thesunRider/RFGen/labRF_Kicad/labRF/labRF.kicad_sch

## KiCad design labRF_Kicad/labRF/labRF.kicad_sch (2024-09-11)

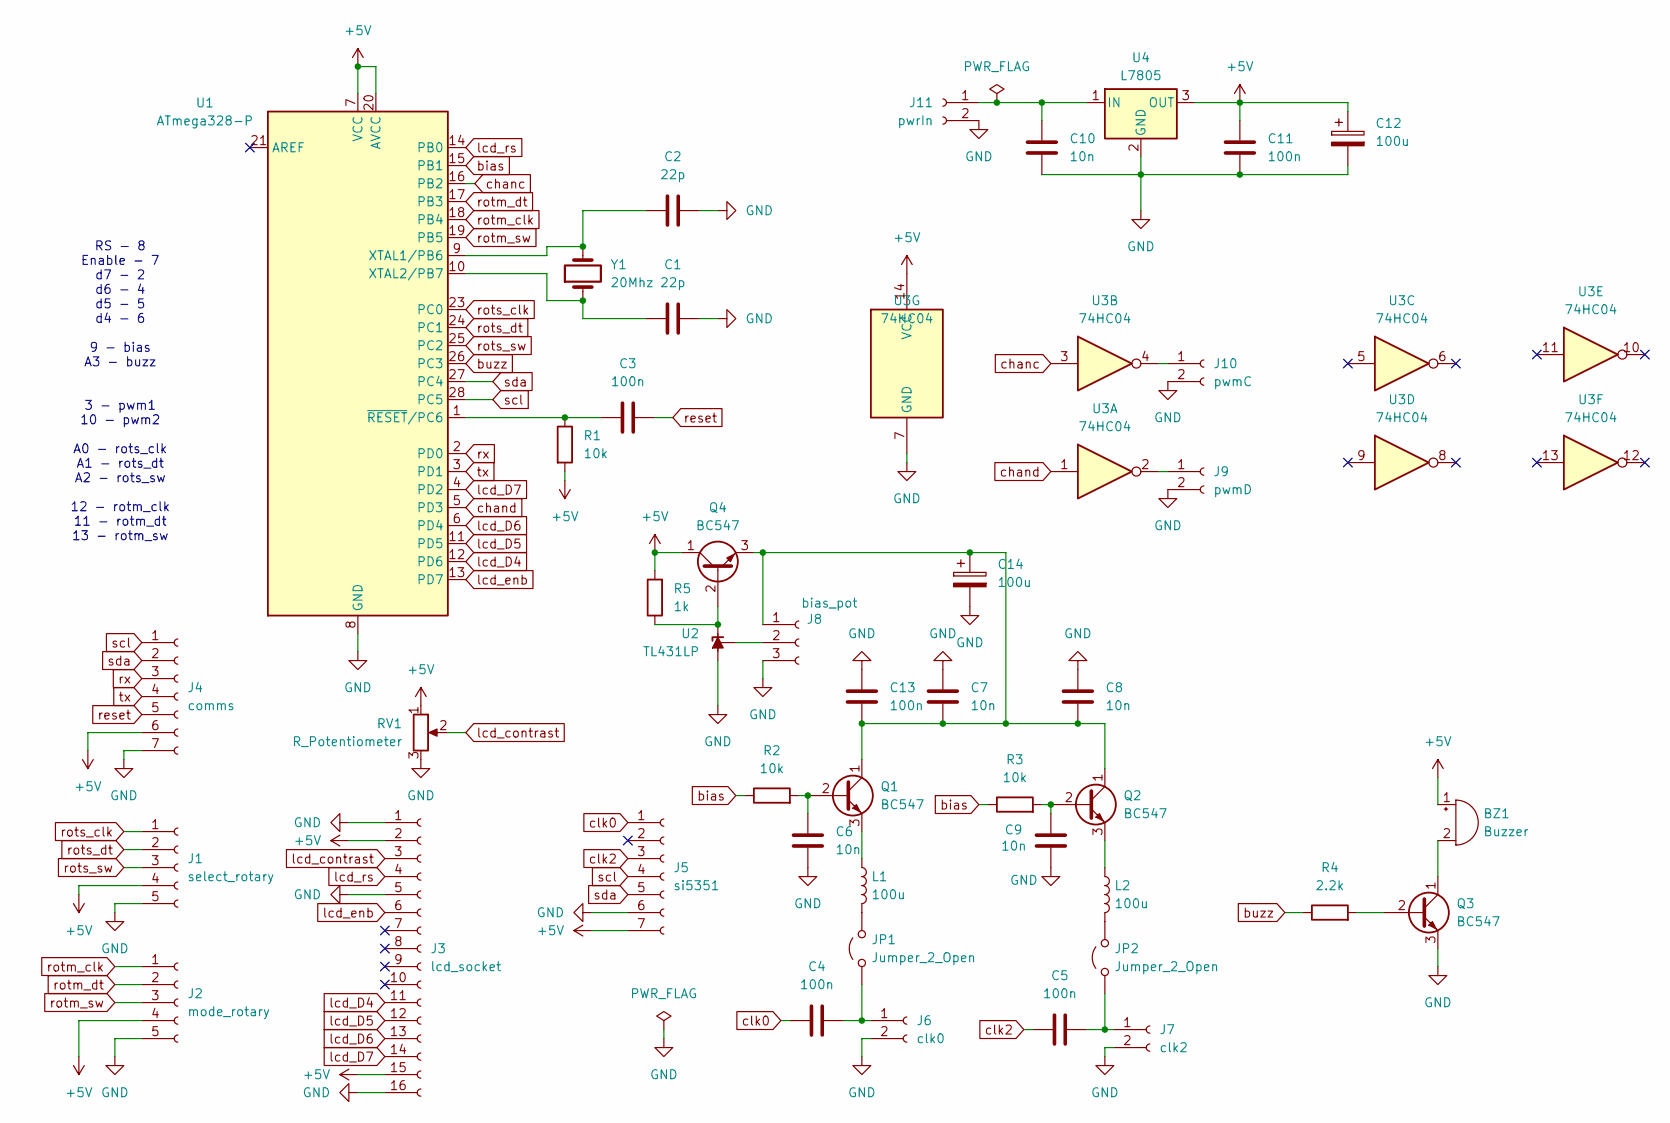
[picture p11: schematic labRF.kicad_sch]

Parts:
BZ1: Buzzer; Buzzer_D14mm_H7mm_P10mm
C1, C2: 22p; C_Disc_D5.0mm_W2.5mm_P2.50mm
C3, C4, C5, C11, C13: 100n; C_Disc_D5.0mm_W2.5mm_P2.50mm
C6, C7, C8, C9, C10: 10n; C_Disc_D5.0mm_W2.5mm_P2.50mm
C12, C14: 100u; CP_Radial_D8.0mm_P5.00mm
J1: select_rotary; PinHeader_1x05_P2.54mm_Vertical
J2: mode_rotary; PinHeader_1x05_P2.54mm_Vertical
J3: lcd_socket; PinHeader_1x16_P2.54mm_Vertical
J4: comms; PinHeader_1x07_P2.54mm_Vertical
J5: si5351; PinHeader_1x07_P2.54mm_Vertical
J6: clk0; PinHeader_1x02_P2.54mm_Vertical
J7: clk2; PinHeader_1x02_P2.54mm_Vertical
J8: bias_pot; FanPinHeader_1x03_P2.54mm_Vertical
J9: pwmD; PinHeader_1x02_P2.54mm_Vertical
J10: pwmC; PinHeader_1x02_P2.54mm_Vertical
J11: pwrIn; PinHeader_1x02_P2.54mm_Vertical
JP1, JP2: Jumper_2_Open; PinHeader_1x02_P2.54mm_Vertical
L1, L2: 100u; L_Toroid_Vertical_L14.7mm_W8.6mm_P5.58mm_Pulse_KM-1
Q1, Q2, Q3, Q4: BC547; TO-92_Inline
R1, R2, R3: 10k; R_Axial_DIN0207_L6.3mm_D2.5mm_P10.16mm_Horizontal
R4: 2.2k; R_Axial_DIN0207_L6.3mm_D2.5mm_P10.16mm_Horizontal
R5: 1k; R_Axial_DIN0207_L6.3mm_D2.5mm_P10.16mm_Horizontal
RV1: R_Potentiometer; Potentiometer_Bourns_3386P_Vertical
U1: ATmega328-P; DIP-28_W7.62mm
U2: TL431LP; TO-92_Inline
U3: 74HC04; DIP-14_W7.62mm
U4: L7805; TO-220-3_Vertical
Y1: 20Mhz; Crystal_HC49-U_Vertical

Connections:
+5V: BZ1.1 (+), C11.2, C12.1, J1.4, J2.4, J3.2, J3.15, J4.6, J5.7, Q4.1 (C), R1.2, R5.2, RV1.1, U1.7 (VCC), U1.20 (AVCC), U3.14 (VCC), U4.3 (OUT)
GND: C1.2, C2.2, C6.2, C7.1, C8.1, C9.2, C10.1, C11.1, C12.2, C13.1, C14.2, J1.5, J2.5, J3.1, J3.5, J3.16, J4.7, J5.6, J6.2, J7.2, J8.3, J9.2, J10.2, J11.2, Q3.3 (E), RV1.3, U1.8 (GND), U1.22 (GND), U2.2 (A), U3.7 (GND), U4.2 (GND)
unnamed: BZ1.2 (-), Q3.1 (C)
unnamed: C1.1, U1.10 (XTAL2/PB7), Y1.1
unnamed: C2.1, U1.9 (XTAL1/PB6), Y1.2
unnamed: C3.1, R1.1, U1.1 (~RESET/PC6)
unnamed: C4.2, J6.1, JP1.1 (A)
unnamed: C5.2, J7.1, JP2.1 (A)
unnamed: C6.1, Q1.2 (B), R2.2
unnamed: C9.1, Q2.2 (B), R3.2
unnamed: C10.2, J11.1, U4.1 (IN)
unnamed: C7.2, C8.2, C13.2, C14.1, J8.1, Q1.1 (C), Q2.1 (C), Q4.3 (E)
unnamed: J8.2, U2.1 (REF)
unnamed: J9.1, U3.2
unnamed: J10.1, U3.4
unnamed: JP1.2 (B), L1.2
unnamed: JP2.2 (B), L2.2
unnamed: L1.1, Q1.3 (E)
unnamed: L2.1, Q2.3 (E)
unnamed: Q3.2 (B), R4.2
unnamed: Q4.2 (B), R5.1, U2.3 (K)
bias: R2.1, R3.1, U1.15 (PB1)
buzz: R4.1, U1.26 (PC3)
chanc: U1.16 (PB2), U3.3
chand: U1.5 (PD3), U3.1
clk0: C4.1, J5.1
clk2: C5.1, J5.3
lcd_D4: J3.11, U1.12 (PD6)
lcd_D5: J3.12, U1.11 (PD5)
lcd_D6: J3.13, U1.6 (PD4)
lcd_D7: J3.14, U1.4 (PD2)
lcd_contrast: J3.3, RV1.2
lcd_enb: J3.6, U1.13 (PD7)
lcd_rs: J3.4, U1.14 (PB0)
reset: C3.2, J4.5
rotm_clk: J2.1, U1.18 (PB4)
rotm_dt: J2.2, U1.17 (PB3)
rotm_sw: J2.3, U1.19 (PB5)
rots_clk: J1.1, U1.23 (PC0)
rots_dt: J1.2, U1.24 (PC1)
rots_sw: J1.3, U1.25 (PC2)
rx: J4.3, U1.2 (PD0)
scl: J4.1, J5.4, U1.28 (PC5)
sda: J4.2, J5.5, U1.27 (PC4)
tx: J4.4, U1.3 (PD1)

Notes on the sheet:
RS - 8 Enable - 7 d7 - 2 d6 - 4 d5 - 5 d4 - 6 9 - bias A3 - buzz 3 - pwm1 10 - pwm2 A0 - rots_clk A1 - rots_dt A2 - rots_sw 12 - rotm_clk 11 - rotm_dt 13 - rotm_sw
