thesunRider/RFGen/sketches/bluepill/main/src/RFM119/HopeDuino_CMT211xA.cpp

/*
 * THE FOLLOWING FIRMWARE IS PROVIDED: 
 *  (1) "AS IS" WITH NO WARRANTY; 
 *  (2) TO ENABLE ACCESS TO CODING INFORMATION TO GUIDE AND FACILITATE CUSTOMER.
 * CONSEQUENTLY, HopeRF SHALL NOT BE HELD LIABLE FOR ANY DIRECT, INDIRECT OR
 * CONSEQUENTIAL DAMAGES WITH RESPECT TO ANY CLAIMS ARISING FROM THE CONTENT
 * OF SUCH FIRMWARE AND/OR THE USE MADE BY CUSTOMERS OF THE CODING INFORMATION
 * CONTAINED HEREIN IN CONNECTION WITH THEIR PRODUCTS.
 * 
 * Copyright (C) HopeRF
 *
 * website: www.HopeRF.com
 *          www.HopeRF.cn     
 */

/*! 
 * file       HopeDuino_CMT211xA.cpp
 * brief      driver for CMT211xA 
 * hardware   HopeDuino with RFM11x
 *            
 *
 * version    1.0
 * date       Feb 18 2016
 * author     QY Ruan
 */

#include "HopeDuino_CMT211xA.h"

/**********************************************************
 **Name:     vCMT211xAInit
 **Function: Init. CMT211xA
 **Input:    none
 **Output:   none
 **********************************************************/
void cmt211xaClass::cmt211xaClass::vCMT211xAInit(void) {
  Twi.vTWIInit();

  Twi.vTWIReset(); //step 1
  vSoftReset(); //step 2
  vTwiOff(); //step 3

  ClrTDAT(); //Set Dat to low
  OutputTDAT(); //Read for Tx
}

//added extra
void cmt211xaClass::TWI_RAM1(uint8_t addr, uint16_t data)
{	
	Twi.vTWIWrite(0x18, addr);
	Twi.vTWIWrite(0x19, data&0xff);
	Twi.vTWIWrite(0x1A, data>>8);
	Twi.vTWIWrite(0x25, 0x01);
}

void cmt211xaClass::turnOnRadio(void) {
  
  Twi.vTWIInit();
  Twi.vTWIReset(); //step 1
  vTwiOff(); //step 2
  SetTDAT();
}

void cmt211xaClass::turnOFFRadio(void) {
ClrTDAT();
}

//added extra
//one register remains unclear after a very rudimentary reverse engineering attempt (0x5f1e gets changed at low frequencies - is this critical?
//frequency = 26000000/2^17/prescale*pll_multiple
//prescale can be 1.5, 2, 3 controlled by positions 1 and 6
//gmsk not supported presently
void cmt211xaClass::vChipfrequency(uint32_t freq, uint32_t dev, uint8_t mod) {
  //determine prescale
  uint8_t prescale15;
  uint8_t prescale2;
  if (freq <= 300000000UL) {
    prescale15 = 1;
    prescale2 = 1;
  } else if (freq <= 400000000UL) {
    prescale15 = 0;
    prescale2 = 1;
  } else if (freq <= 600000000UL) {
    prescale15 = 1;
    prescale2 = 0;
  } else {
    prescale15 = 0;
    prescale2 = 0;
  }

  if (prescale15) TWI_RAM1(6, 0x0001);
  if (prescale2) TWI_RAM1(1, 0x5400);

  int8_t psc2 = 0;
  if (prescale15) psc2 -= 1;
  if (prescale2) psc2 += 1;

  //frequency
  uint64_t tmp1 = freq;
  tmp1 <<= 17 + psc2;
  if (prescale15) tmp1 *= 3;
  uint32_t pll = tmp1 / 26000000UL;
  TWI_RAM1(7, pll & 0xffff);
  TWI_RAM1(8, ((pll >> 16) << 8) | 0x08);

  if (mod == 2) {
    //deviation
    tmp1 = dev;
    tmp1 <<= 14 + psc2;
    if (prescale15) tmp1 *= 3;
    pll = tmp1 / 26000000UL;
    pll <<= 3;
    pll &= 0x07f8;
  } else pll = 0; //no deviation in ook
  TWI_RAM1(9, pll);
}

/**********************************************************
 **Name:     vCMT2119AInit
 **Function: Init. CMT2119A with config 
 **Input:    none
 **Output:   none
 **********************************************************/
void cmt211xaClass::vCMT2119AInit(word para[], byte length,uint32_t freq, uint32_t dev, uint8_t mod)  {
  byte i;
  Twi.vTWIInit();

  Twi.vTWIReset(); //step 1
  vSoftReset(); //step 2
  delay(2); //wait more than 1ms		
  vOpenLdoAndOsc(); //step 3
  vActiveRegsister(); //step 4
  vEnableRegMode(); //step 5
  for (i = 0; i < length; i++) //step 6
    vWriteReg(i, para[i]);

  //reprogram frequency
  vChipfrequency(freq, dev, mod);

  vTwiOff(); //step 7	

  ClrTDAT(); //Set Dat to low
  OutputTDAT(); //Read for Tx
}

/**********************************************************
 **Name:     vCMT211xASleep
 **Function: set CMT211xA to sleep
 **Input:    none
 **Output:   none
 **********************************************************/
void cmt211xaClass::vCMT211xASleep(void) {
  Twi.vTWIReset(); //step 1
  vSoftReset(); //step 2
}

/**********************************************************
 **Name:     vCMT2119ASleep
 **Function: set CMT2119A to sleep
 **Input:    none
 **Output:   none
 **********************************************************/
void cmt211xaClass::vCMT2119ASleep(void) {
  vCloseLdoAndOsc(); //step 1
  Twi.vTWIReset(); //step 2
  vSoftReset(); //step 3
}

/**********************************************************
**Name:     vEncode
**Function: encode 
**Input:    ptr��length��etype
            length need less than 64
**Output:   TxBuf
**********************************************************/
void cmt211xaClass::vEncode(byte ptr[], byte length, encodeType etype) {
  byte i, j, k;

  switch (etype) {
  case E527:
    TxBuf[0] = 0x80;
    TxBuf[1] = 0x00;
    TxBuf[2] = 0x00;
    TxBuf[3] = 0x00;
    for (i = 4; i < (4 + (length << 2)); i++) //1XX0
      TxBuf[i] = 0x88;
    k = 4;
    for (j = 0; j < length; j++) {
      for (i = 0x80; i != 0;) {
        if ((ptr[j] & i) != 0)
          TxBuf[k] |= 0x60;
        i >>= 1;
        if ((ptr[j] & i) != 0)
          TxBuf[k] |= 0x06;
        i >>= 1;
        k++;
      }
    }
    TxBufLength = ((length << 2) + 4);
    break;
  case E201:
    for (i = 0; i < 4; i++) //
      TxBuf[i] = 0x00; //4 byte 0x00
    TxBuf[4] = 0x0A; //10 pulse preamble	
    for (i = 5; i < (5 + 2); i++)
      TxBuf[i] = 0xAA;
    TxBuf[i++] = 0x00; //Sync
    TxBuf[i++] = 0x00;
    k = i + (length * 3);
    j = i;
    for (; j < k;) {
      TxBuf[j++] = 0x92; //1x01x01xB
      TxBuf[j++] = 0x49; //01x01x01B
      TxBuf[j++] = 0x24; //x01x01x0B
    }

    for (j = 0; j < length; j++) {
      if ((ptr[j] & 0x80) == 0x00)
        TxBuf[i] |= 0x40;
      if ((ptr[j] & 0x40) == 0x00)
        TxBuf[i] |= 0x08;
      if ((ptr[j] & 0x20) == 0x00)
        TxBuf[i] |= 0x01;
      i++;
      if ((ptr[j] & 0x10) == 0x00)
        TxBuf[i] |= 0x20;
      if ((ptr[j] & 0x08) == 0x00)
        TxBuf[i] |= 0x04;
      i++;
      if ((ptr[j] & 0x04) == 0x00)
        TxBuf[i] |= 0x80;
      if ((ptr[j] & 0x02) == 0x00)
        TxBuf[i] |= 0x10;
      if ((ptr[j] & 0x01) == 0x00)
        TxBuf[i] |= 0x02;
      i++;
    }
    TxBuf[i++] = 0x92;
    TxBufLength = i;
    break;
  case ENRZ:
  default:
    for (i = 0; i < length; i++) //do nothing
      TxBuf[i] = ptr[i];
    TxBufLength = length;
    break;
  }
}

//**********************HAL Layer**************************
/**********************************************************
 **Name:     vOpenLdoAndOsc
 **Function: Open LDO & Osc(only for CMT2119A)
 **Input:    none
 **Output:   none
 **********************************************************/
void cmt211xaClass::vOpenLdoAndOsc(void) {
  if (Chipset == CMT2119A)
    Twi.vTWIWrite(0x02, 0x78);
}

/**********************************************************
 **Name:     vCloseLdoAndOsc
 **Function: Close LDO & Osc (only for CMT2119A)
 **Input:    none
 **Output:   none
 **********************************************************/
void cmt211xaClass::vCloseLdoAndOsc(void) {
  if (Chipset == CMT2119A)
    Twi.vTWIWrite(0x02, 0x7F);
}

/**********************************************************
 **Name:     vActiveRegsister
 **Function: Active Regsisiter Mode (Step-4)  (only for CMT2119A)
 **Input:    none
 **Output:   none
 **********************************************************/
void cmt211xaClass::vActiveRegsister(void) {
  if (Chipset == CMT2119A) {
    Twi.vTWIWrite(0x2F, 0x80);
    Twi.vTWIWrite(0x35, 0xCA);
    Twi.vTWIWrite(0x36, 0xEB);
    Twi.vTWIWrite(0x37, 0x37);
    Twi.vTWIWrite(0x38, 0x82);
  }
}

/**********************************************************
 **Name:     EnableRegMode
 **Function: Active Enable Regsisiter Mode (Step-5)  (only for CMT2119A)
 **Input:    none
 **Output:   none
 **********************************************************/
void cmt211xaClass::vEnableRegMode(void) {
  if (Chipset == CMT2119A) {
    Twi.vTWIWrite(0x12, 0x10);
    Twi.vTWIWrite(0x12, 0x00);
    Twi.vTWIWrite(0x24, 0x07);
    Twi.vTWIWrite(0x1D, 0x20);
  }
}

/**********************************************************
 **Name:     vWriteReg
 **Function: wirte something to Regsisiter  (only for CMT2119A)
 **Input:    none
 **Output:   none
 **********************************************************/
void cmt211xaClass::vWriteReg(byte adr, word wrPara) {
  if (Chipset == CMT2119A) {
    Twi.vTWIWrite(0x18, adr);
    Twi.vTWIWrite(0x19, (byte) wrPara);
    Twi.vTWIWrite(0x1A, (byte)(wrPara >> 8));
    Twi.vTWIWrite(0x25, 0x01);
  }
}

/**********************************************************
 **Name:     vReadReg
 **Function: read something from Regsisiter 	(only for CMT2119A)
 **Input:    none
 **Output:   none
 **********************************************************/
word cmt211xaClass::wReadReg(byte adr) {
  byte i_H, i_L;
  if (Chipset == CMT2119A) {
    Twi.vTWIWrite(0x18, adr);
    i_L = Twi.bTWIRead(0x1b);
    i_H = Twi.bTWIRead(0x1c);
    return (((word) i_H) << 8 | i_L);
  } else
    return (0);
}

/**********************************************************
 **Name:     vSoftReset
 **Function: Software Reset Chipset
 **Input:    none
 **Output:   none
 **********************************************************/
void cmt211xaClass::vSoftReset(void) {
  Twi.vTWIWrite(0x3D, 0x01); //0xBD01
}

/**********************************************************
 **Name:     vTwiReset
 **Function: Twi mode on
 **Input:    none
 **Output:   none
 **********************************************************/
void cmt211xaClass::vTwiReset(void) {
  Twi.vTWIReset();
}

/**********************************************************
 **Name:     vTwiOff
 **Function: Twi mode off
 **Input:    none
 **Output:   none
 **********************************************************/
void cmt211xaClass::vTwiOff(void) {
  Twi.vTWIWrite(0x0D, 0x02); //0x8D02
}
